bitwisebones/switcher/schematic/remote-switcher.kicad_sch

## KiCad design schematic/remote-switcher.kicad_sch (2025-01-18)

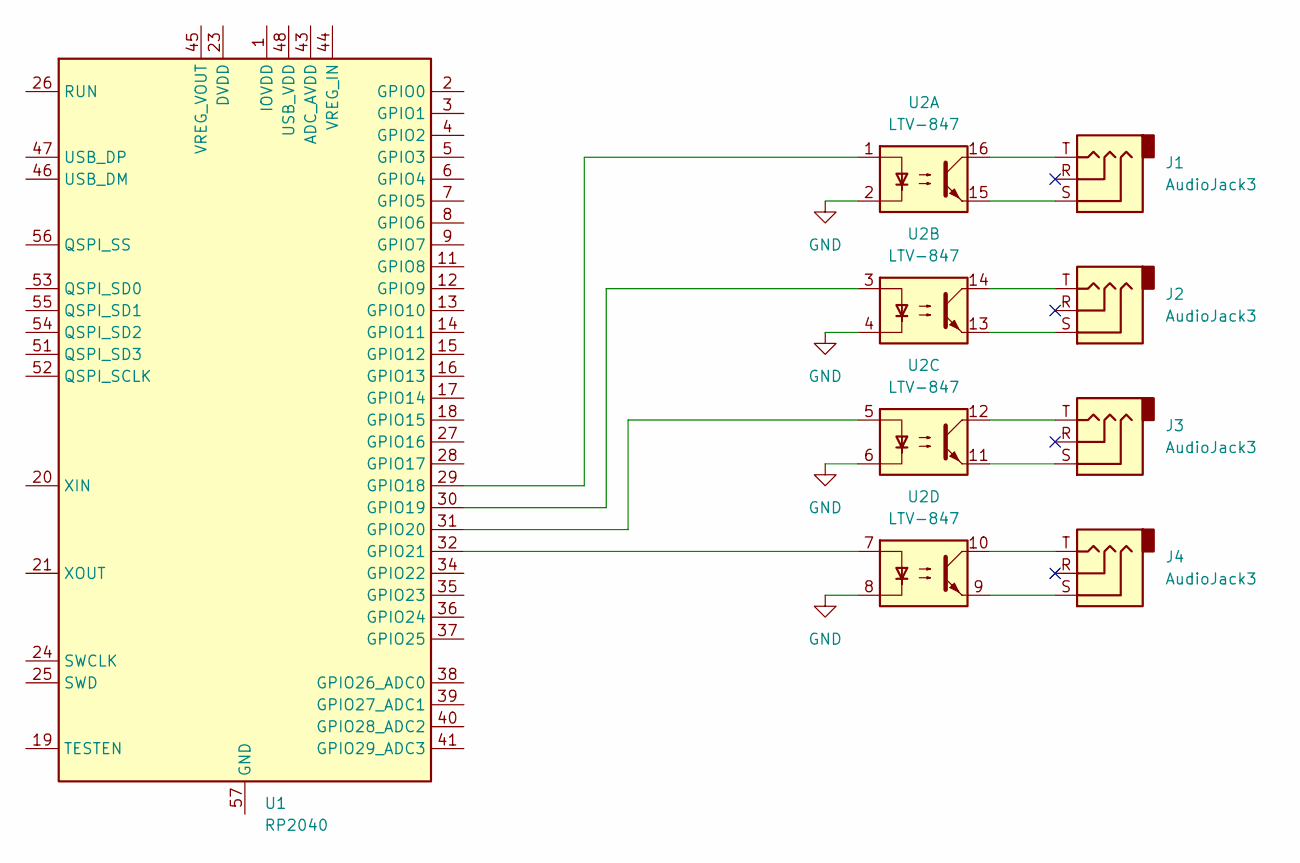
[picture p6: schematic remote-switcher.kicad_sch]

Parts:
J1, J2, J3, J4: AudioJack3
U1: RP2040; QFN-56-1EP_7x7mm_P0.4mm_EP3.2x3.2mm
U2: LTV-847; DIP-6_W7.62mm_Socket

Connections:
GND: U2.2, U2.4, U2.6, U2.8
unnamed: J1.S, U2.15
unnamed: J1.T, U2.16
unnamed: J2.S, U2.13
unnamed: J2.T, U2.14
unnamed: J3.S, U2.11
unnamed: J3.T, U2.12
unnamed: J4.S, U2.9
unnamed: J4.T, U2.10
unnamed: U1.1 (IOVDD), U1.10 (IOVDD), U1.22 (IOVDD), U1.33 (IOVDD), U1.42 (IOVDD), U1.49 (IOVDD)
unnamed: U1.23 (DVDD), U1.50 (DVDD)
unnamed: U1.29 (GPIO18), U2.1
unnamed: U1.30 (GPIO19), U2.3
unnamed: U1.31 (GPIO20), U2.5
unnamed: U1.32 (GPIO21), U2.7
